TUDA-MUST/HELENE/helene_ros/src/hw_description/meshes/Komponente5.stl

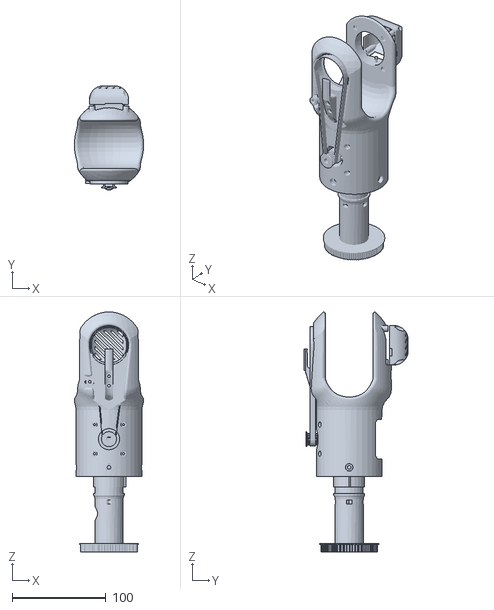
[picture p21: CAD file, 2024-12-10]
helene_ros/src/hw_description/meshes/Komponente5.stl
73.8 x 111.1 x 255.6
