TUDA-MUST/HELENE/hardware_build/print files/col2/B34_Gelenk6_Deckel.stl

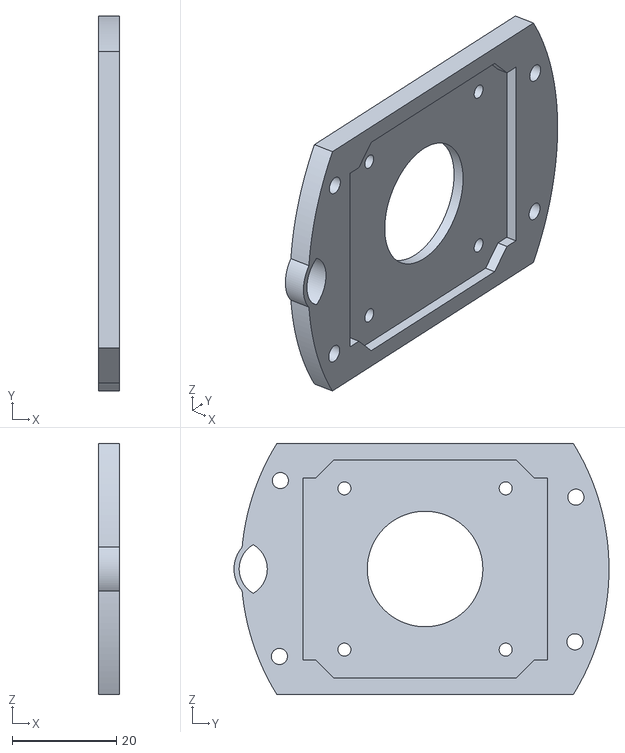
[picture p22: CAD file, 2024-12-10]
hardware_build/print files/col2/B34_Gelenk6_Deckel.stl
4.00 x 72.1 x 48.3
