TUDA-MUST/HELENE/hardware_build/print files/col2/B20_Gelenk3_Welle_Abschluss.stl

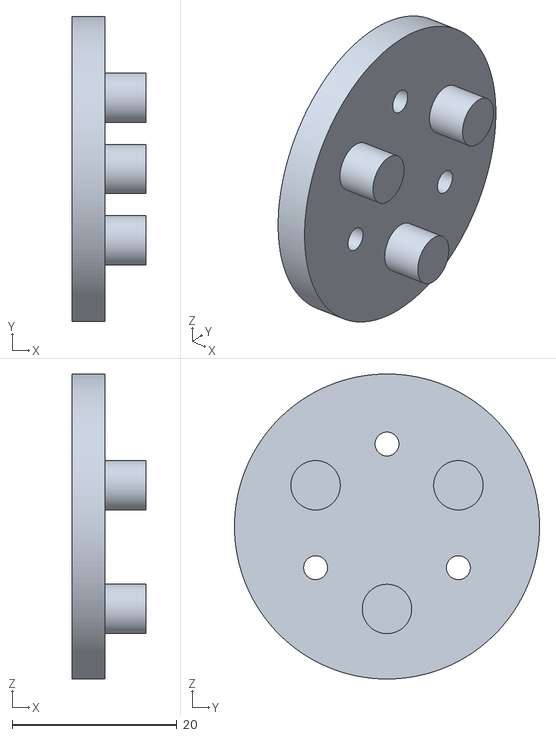
[picture p23: CAD file, 2024-12-10]
hardware_build/print files/col2/B20_Gelenk3_Welle_Abschluss.stl
9.00 x 37.0 x 37.0
