TUDA-MUST/HELENE/hardware_build/print files/col2/B6_Basis_Pulley_klein2.stl

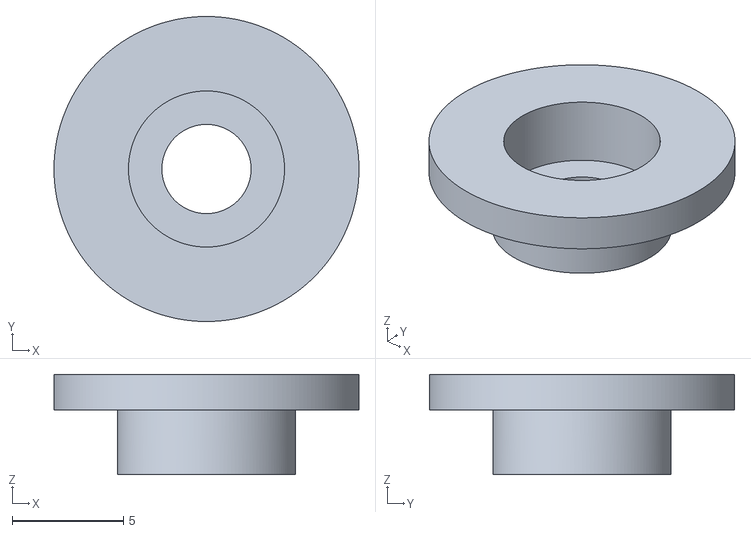
[picture p24: CAD file, 2024-12-10]
hardware_build/print files/col2/B6_Basis_Pulley_klein2.stl
13.7 x 13.7 x 4.50
