TUDA-MUST/HELENE/hardware_build/print files/col2/B7_Basis_Bodenplatte.stl

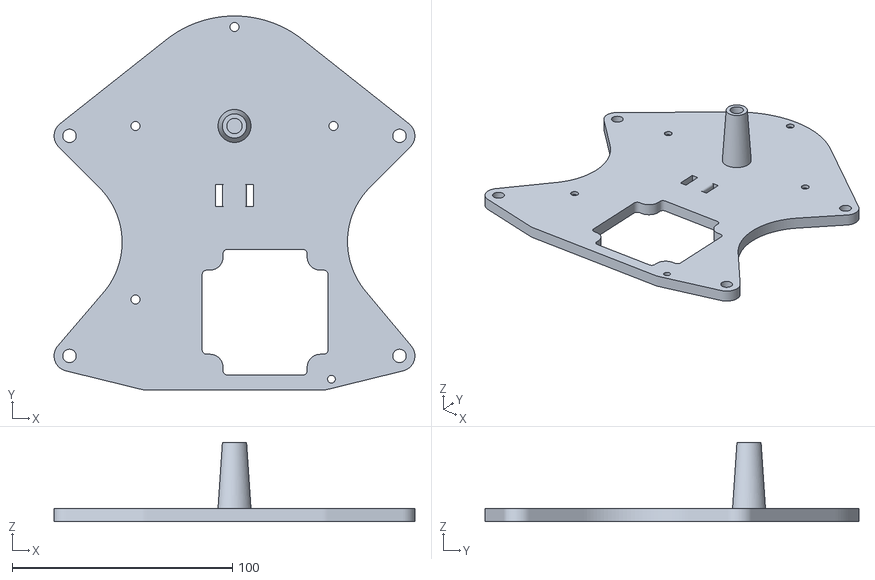
[picture p25: CAD file, 2024-12-10]
hardware_build/print files/col2/B7_Basis_Bodenplatte.stl
164.0 x 170.0 x 36.0
