TUDA-MUST/HELENE/hardware_build/print files/col2/B12_Gelenk2_Festlager_Gelenkfassung.stl

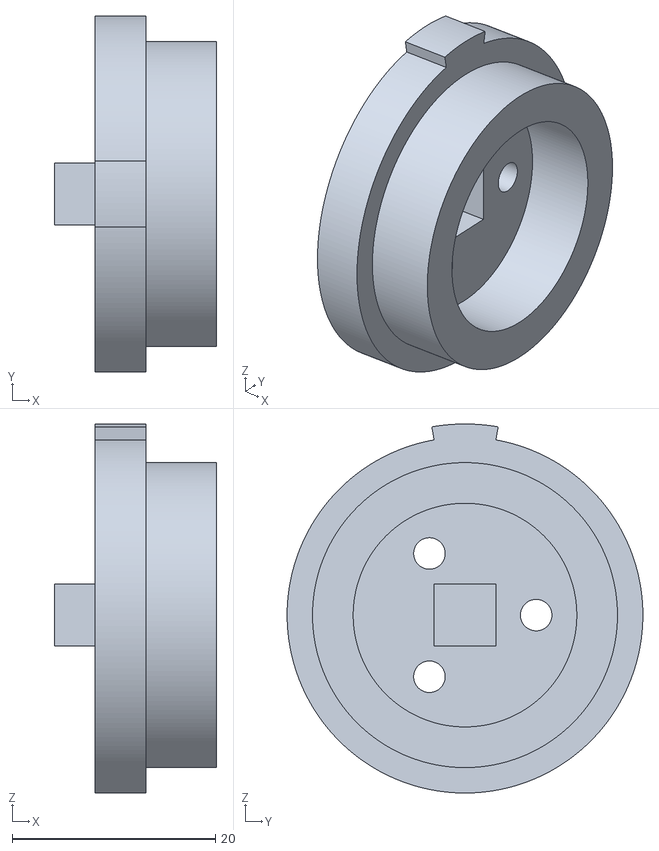
[picture p26: CAD file, 2024-12-10]
hardware_build/print files/col2/B12_Gelenk2_Festlager_Gelenkfassung.stl
15.9 x 35.0 x 36.3
