TUDA-MUST/HELENE/hardware_build/print files/col2/B28_Gelenk4_5_Ubergang.stl

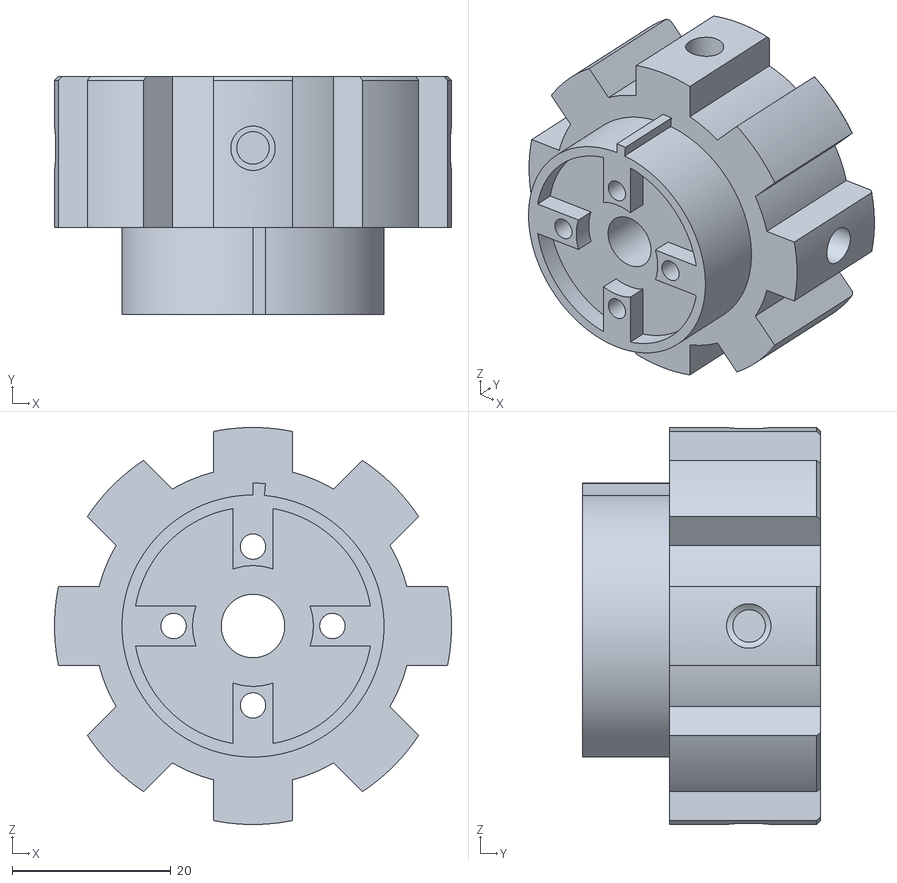
[picture p27: CAD file, 2024-12-10]
hardware_build/print files/col2/B28_Gelenk4_5_Ubergang.stl
50.0 x 30.0 x 50.0
