TUDA-MUST/HELENE/hardware_build/print files/col2/B13_Gelenk2_Welle_Abschluss.stl

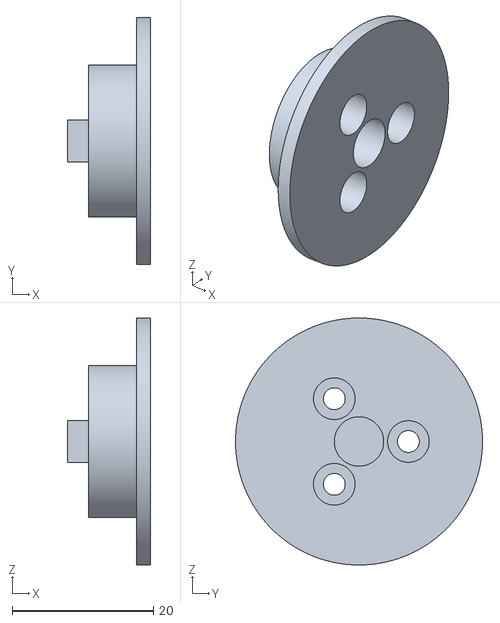
[picture p28: CAD file, 2024-12-10]
hardware_build/print files/col2/B13_Gelenk2_Welle_Abschluss.stl
11.8 x 35.0 x 35.0
