TUDA-MUST/HELENE/hardware_build/print files/col2/B26_Gelenk4_Pulley.stl

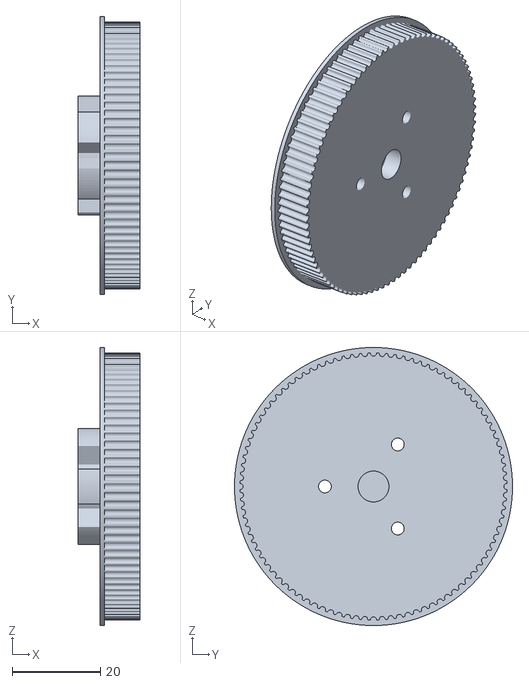
[picture p29: CAD file, 2024-12-10]
hardware_build/print files/col2/B26_Gelenk4_Pulley.stl
14.0 x 63.0 x 63.0
