TUDA-MUST/HELENE/hardware_build/print files/col2/B14_Gelenk2_Lagerdecke.stl

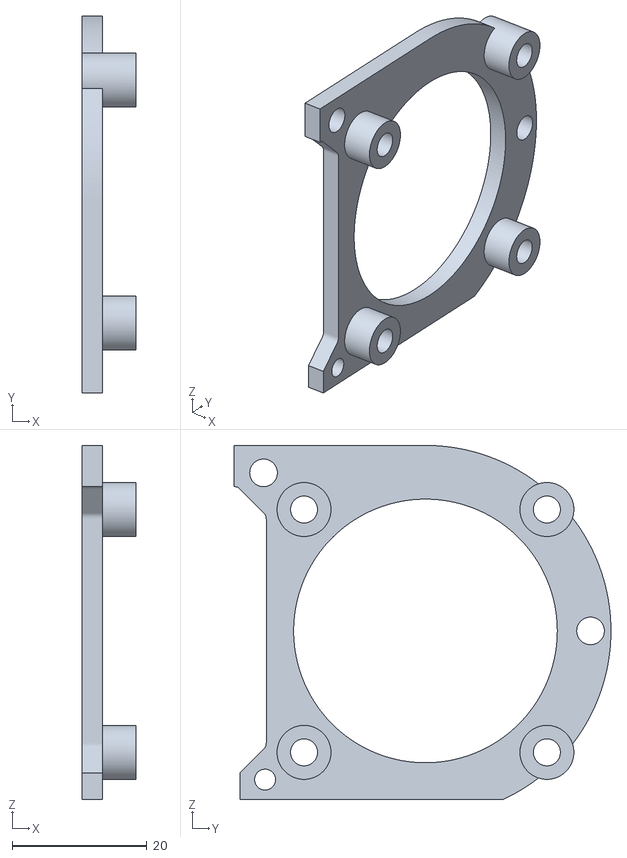
[picture p30: CAD file, 2024-12-10]
hardware_build/print files/col2/B14_Gelenk2_Lagerdecke.stl
8.00 x 55.9 x 52.5
