TUDA-MUST/HELENE/hardware_build/print files/col2/B21_Gelenk3_Motorhalter.stl

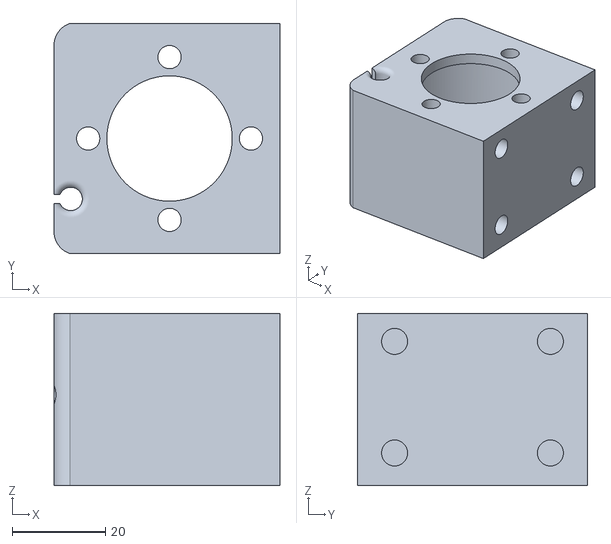
[picture p31: CAD file, 2024-12-10]
hardware_build/print files/col2/B21_Gelenk3_Motorhalter.stl
48.6 x 49.5 x 37.0
