TUDA-MUST/HELENE/hardware_build/print files/col2/B35_Deckel_Elektronik.stl

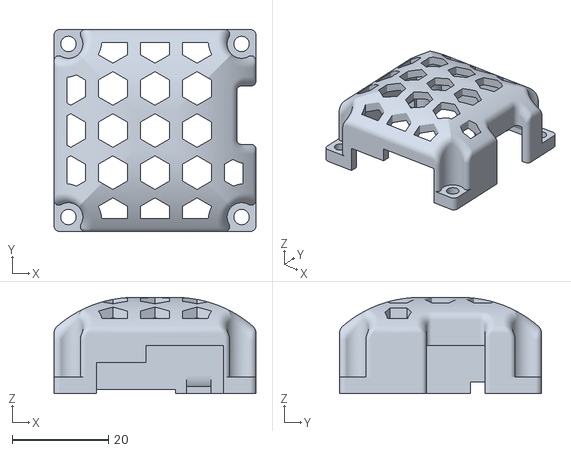
[picture p32: CAD file, 2024-12-10]
hardware_build/print files/col2/B35_Deckel_Elektronik.stl
42.0 x 42.0 x 20.0
