TUDA-MUST/HELENE/hardware_build/print files/col2/B5_Basis_Pulley_klein.stl

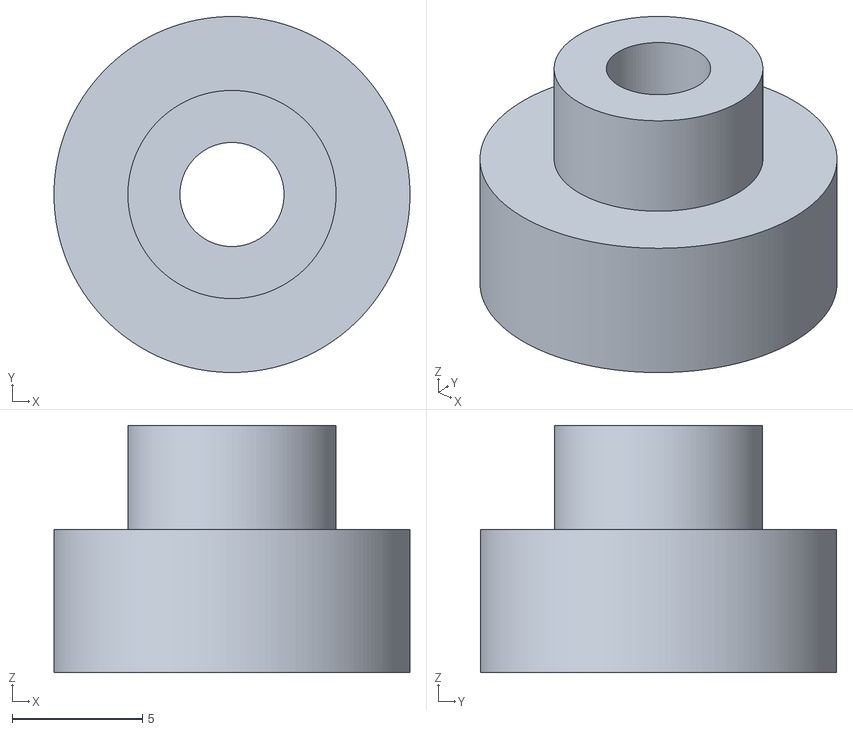
[picture p33: CAD file, 2024-12-10]
hardware_build/print files/col2/B5_Basis_Pulley_klein.stl
13.7 x 13.7 x 9.50
