TUDA-MUST/HELENE/hardware_build/print files/col2/B30_Gelenk5_Welle.stl

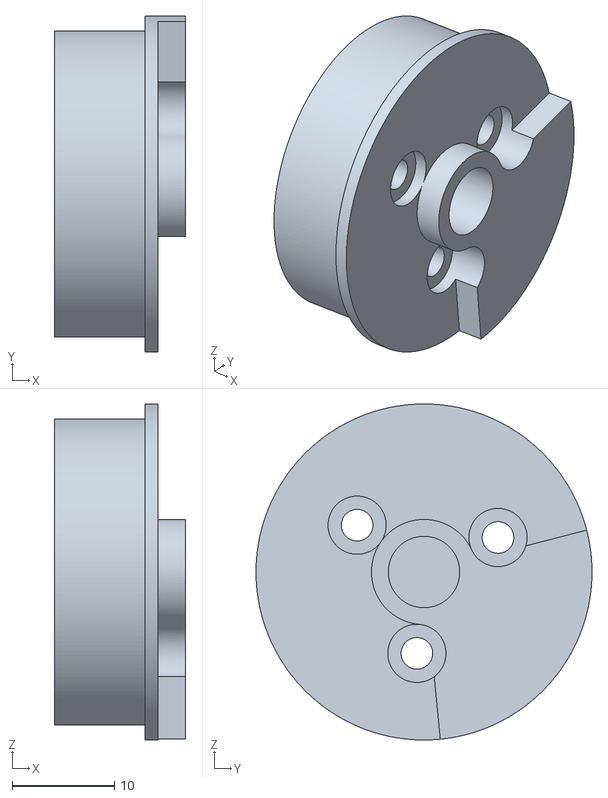
[picture p34: CAD file, 2024-12-10]
hardware_build/print files/col2/B30_Gelenk5_Welle.stl
12.9 x 32.9 x 32.9
